andreabenini/FatBottomedBoard/electronics/teensy++2.0.png

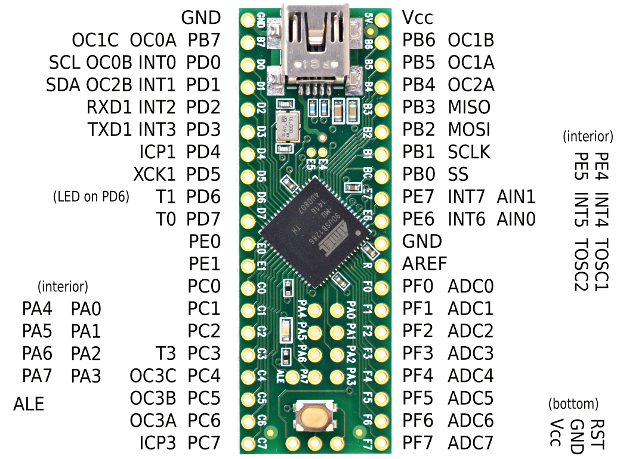
electronics/teensy++2.0.png
