andreabenini/FatBottomedBoard/badassmouse/bam-desk needle.stl

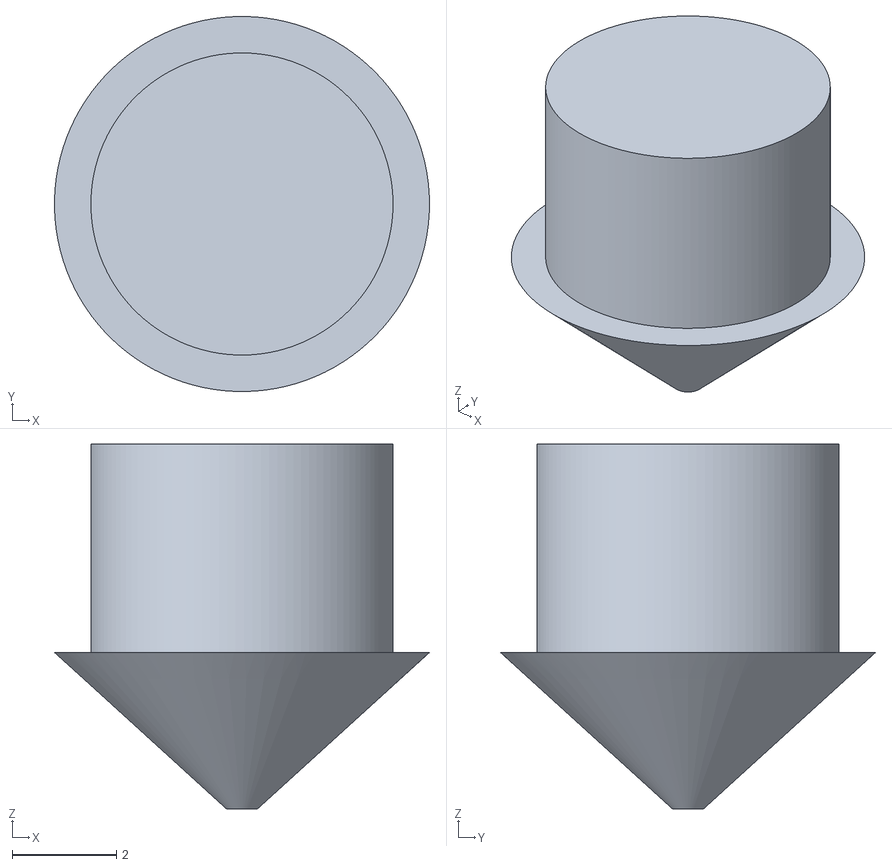
[picture p19: CAD file, 2025-08-23]
badassmouse/bam-desk needle.stl
7.20 x 7.20 x 7.00
