andreabenini/FatBottomedBoard/badassmouse/bam-wheel lock.stl

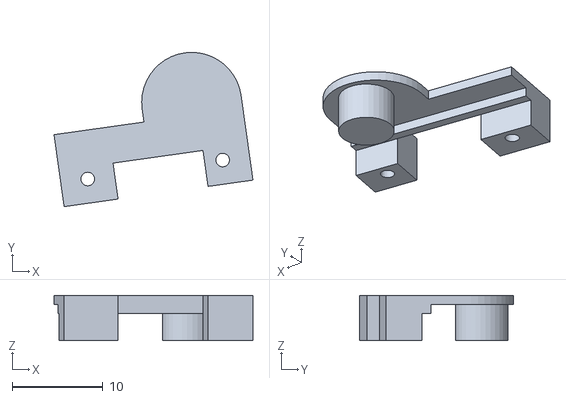
[picture p20: CAD file, 2025-08-15]
badassmouse/bam-wheel lock.stl
21.9 x 17.0 x 5.00
