andreabenini/FatBottomedBoard/badassmouse/bam-cable holder.stl

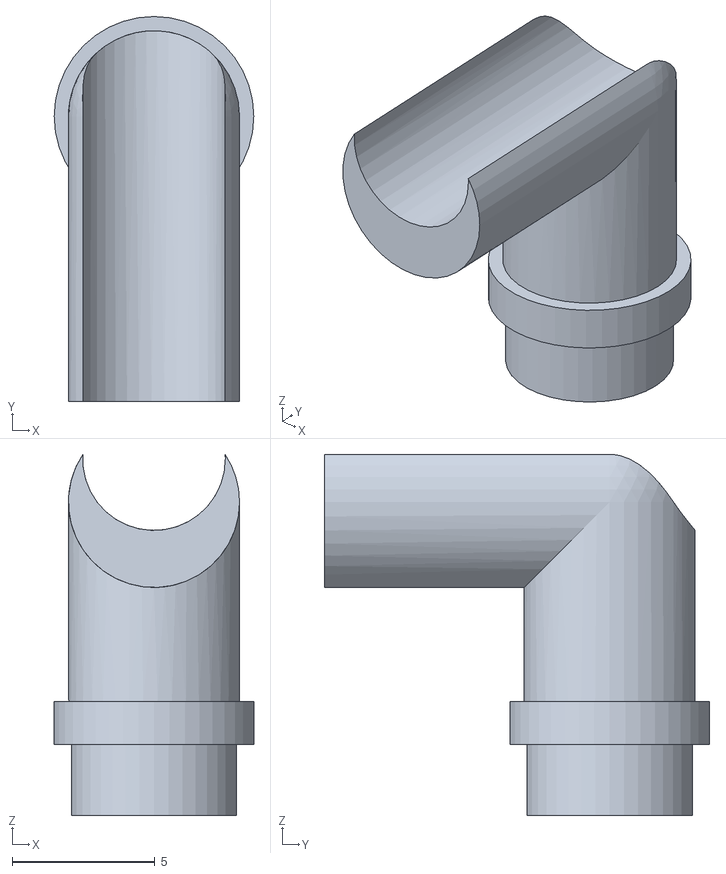
[picture p21: CAD file, 2025-08-13]
badassmouse/bam-cable holder.stl
7.00 x 13.5 x 12.7
