andreabenini/FatBottomedBoard/badassmouse/bam-scroll wheel holder.stl

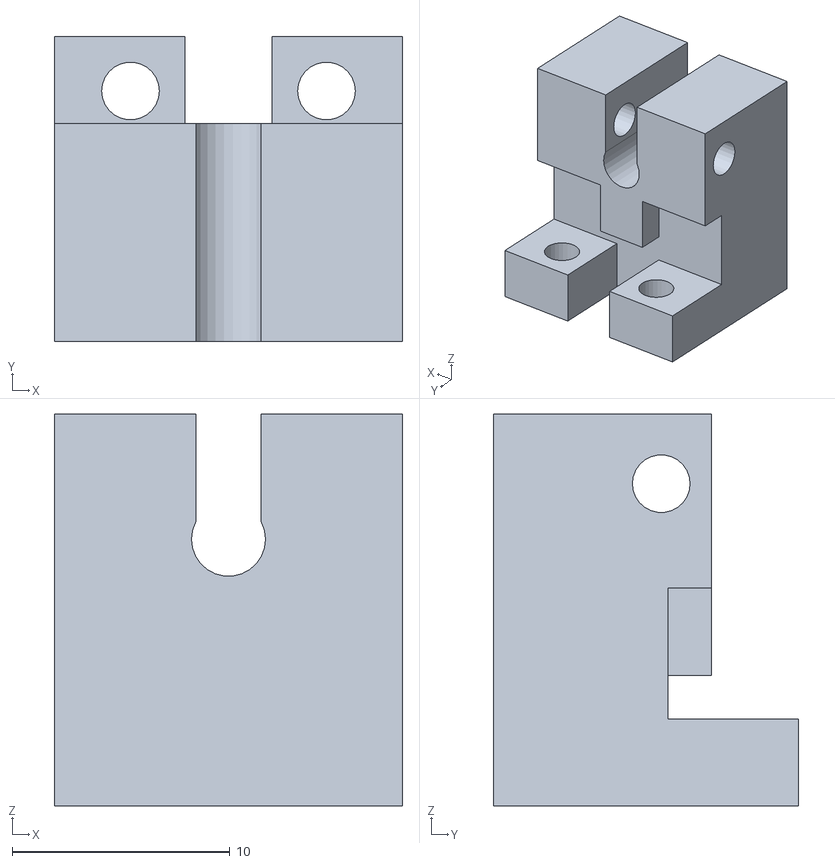
[picture p22: CAD file, 2025-08-13]
badassmouse/bam-scroll wheel holder.stl
16.0 x 14.0 x 18.0
