andreabenini/FatBottomedBoard/badassmouse/bam-support buttons.stl

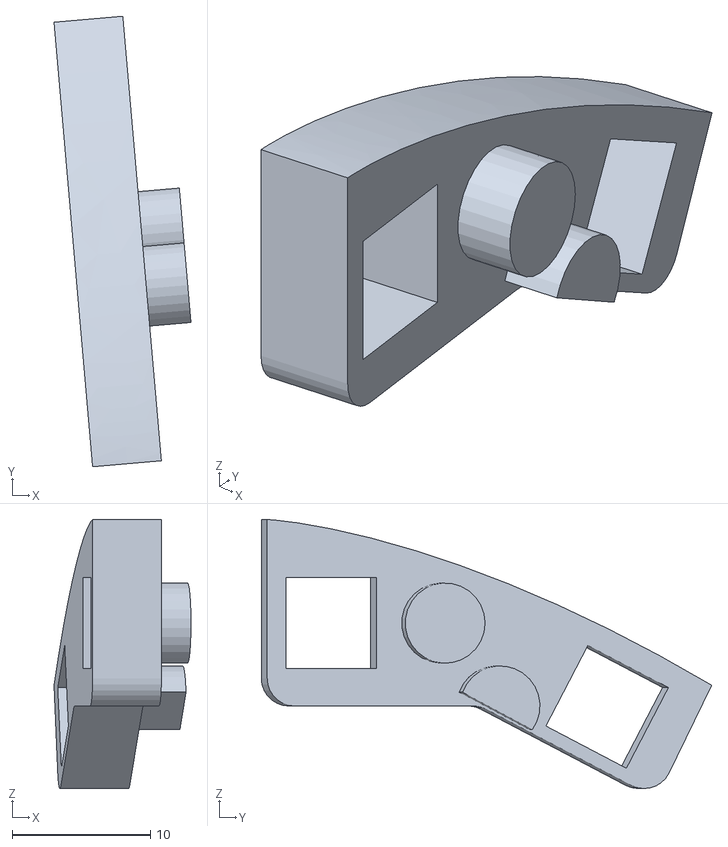
[picture p23: CAD file, 2025-08-09]
badassmouse/bam-support buttons.stl
9.92 x 32.6 x 19.5
