andreabenini/FatBottomedBoard/badassmouse/bam-USB cable holder.stl

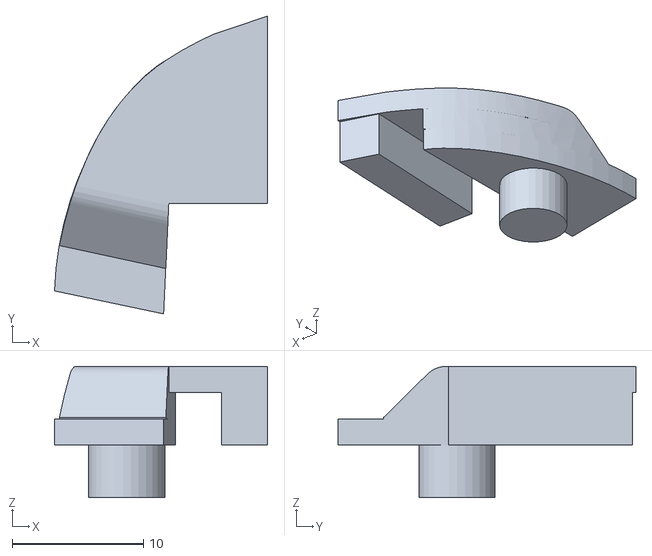
[picture p24: CAD file, 2025-08-09]
badassmouse/bam-USB cable holder.stl
16.2 x 22.7 x 10.0
