andreabenini/FatBottomedBoard/badassmouse/bam-partition back.stl

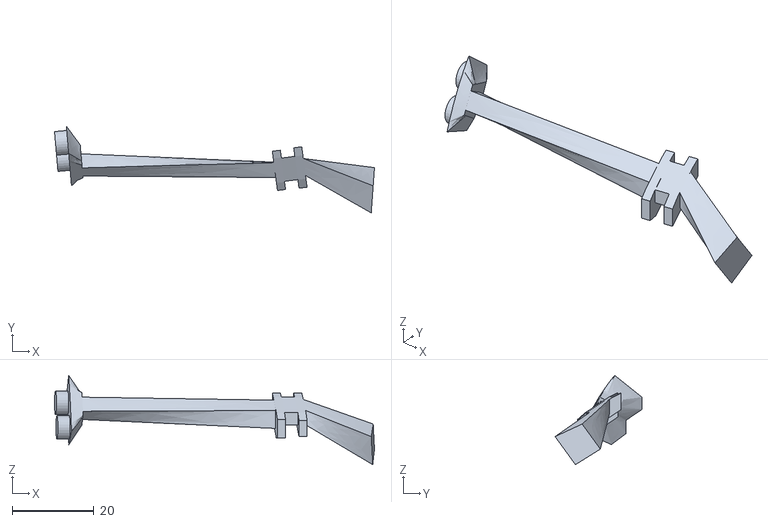
[picture p25: CAD file, 2025-08-08]
badassmouse/bam-partition back.stl
78.4 x 21.3 x 21.9
