andreabenini/FatBottomedBoard/badassmouse/bam-partition pinky right 1.stl

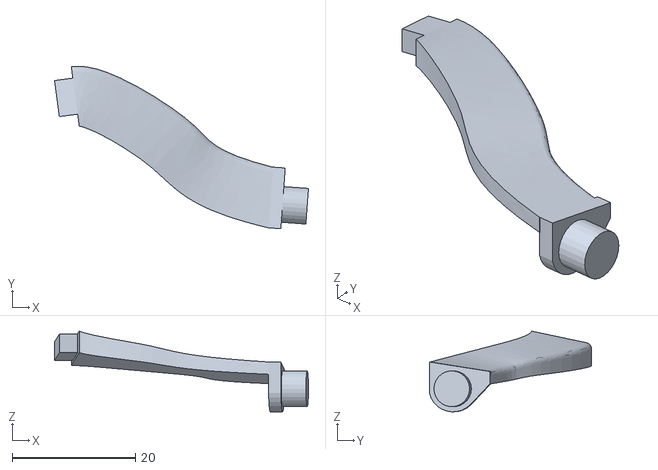
[picture p26: CAD file, 2025-08-06]
badassmouse/bam-partition pinky right 1.stl
41.2 x 26.4 x 13.1
