andreabenini/FatBottomedBoard/badassmouse/bam-bridge right.stl

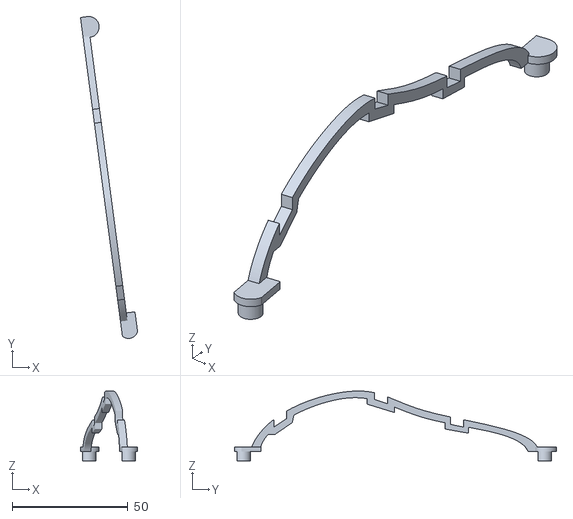
[picture p27: CAD file, 2025-08-06]
badassmouse/bam-bridge right.stl
24.6 x 138.9 x 30.1
