andreabenini/FatBottomedBoard/badassmouse/bam-support 3rd button.stl

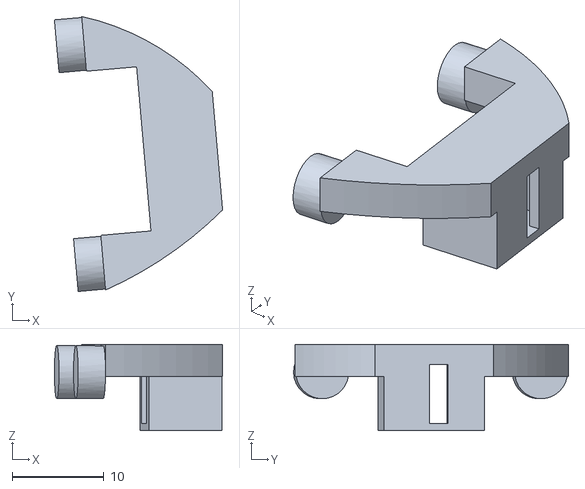
[picture p28: CAD file, 2025-08-04]
badassmouse/bam-support 3rd button.stl
18.4 x 30.0 x 9.45
