andreabenini/FatBottomedBoard/badassmouse/bam-bridge left.stl

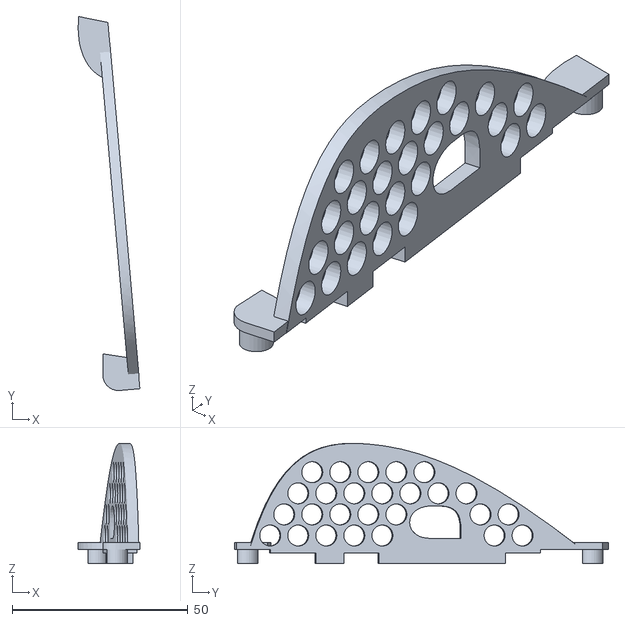
[picture p29: CAD file, 2025-08-04]
badassmouse/bam-bridge left.stl
17.6 x 106.3 x 34.2
