andreabenini/FatBottomedBoard/badassmouse/bam-bridge pinky.stl

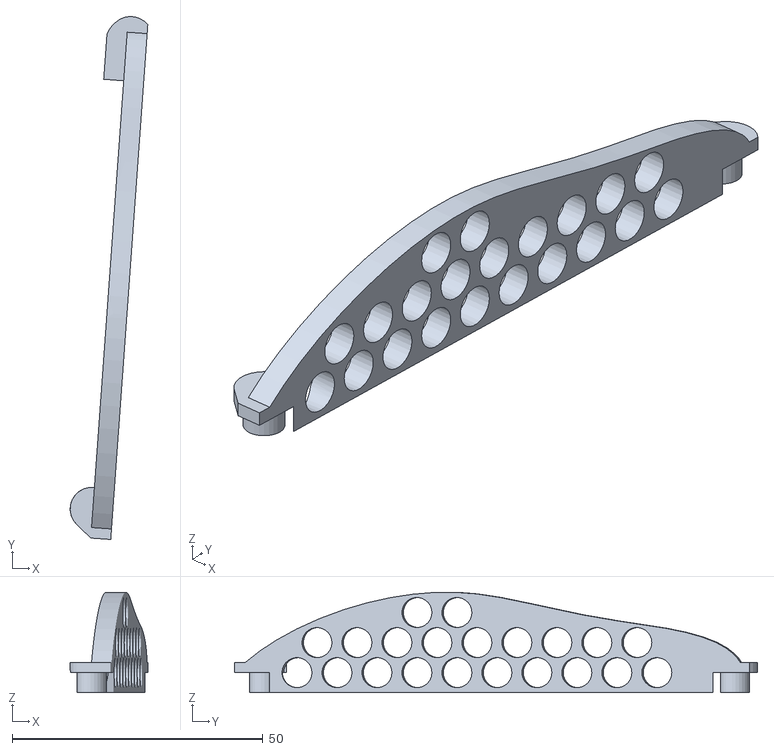
[picture p30: CAD file, 2025-08-04]
badassmouse/bam-bridge pinky.stl
15.5 x 104.4 x 20.0
