andreabenini/FatBottomedBoard/badassmouse/bam-3rd button.stl

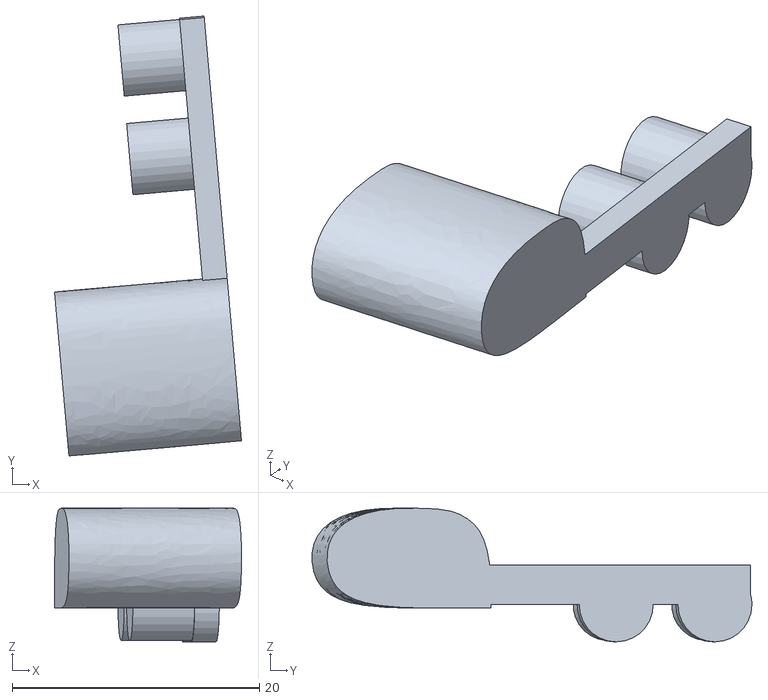
[picture p31: CAD file, 2025-08-04]
badassmouse/bam-3rd button.stl
15.1 x 35.6 x 10.8
