andreabenini/FatBottomedBoard/badassmouse/bam-pcb holder.stl

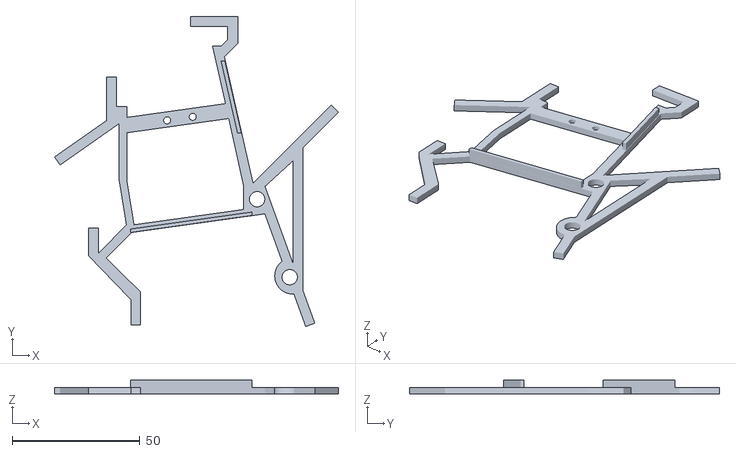
[picture p32: CAD file, 2025-07-30]
badassmouse/bam-pcb holder.stl
111.1 x 121.3 x 5.50
