andreabenini/FatBottomedBoard/badassmouse/bam-Palm connection.stl

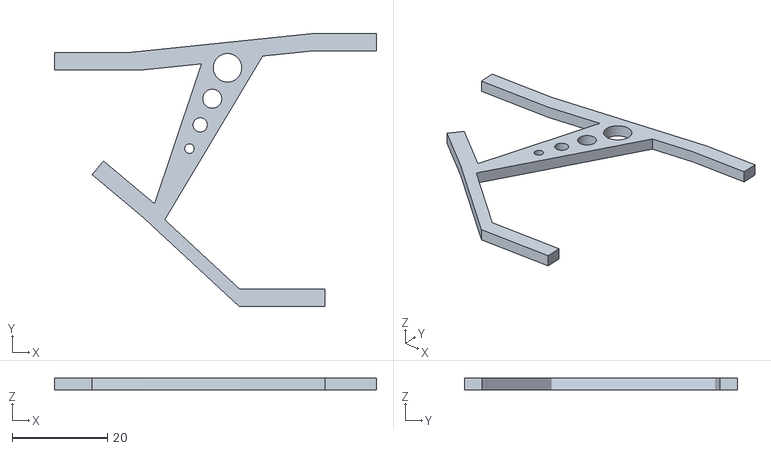
[picture p33: CAD file, 2025-07-30]
badassmouse/bam-Palm connection.stl
67.8 x 57.5 x 2.50
