andreabenini/FatBottomedBoard/badassmouse/bam-Ring and Pinky.stl

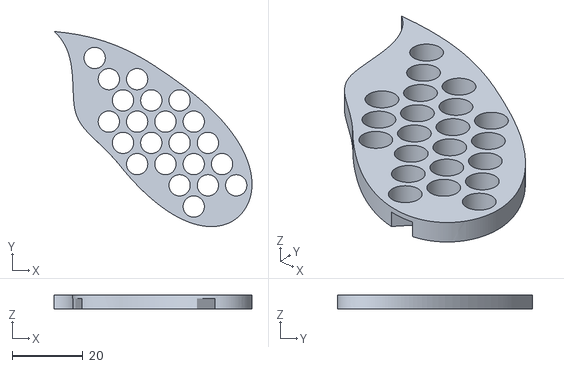
[picture p34: CAD file, 2025-07-29]
badassmouse/bam-Ring and Pinky.stl
56.0 x 55.2 x 4.00
