andreabenini/FatBottomedBoard/badassmouse/bam-Left and Right.stl

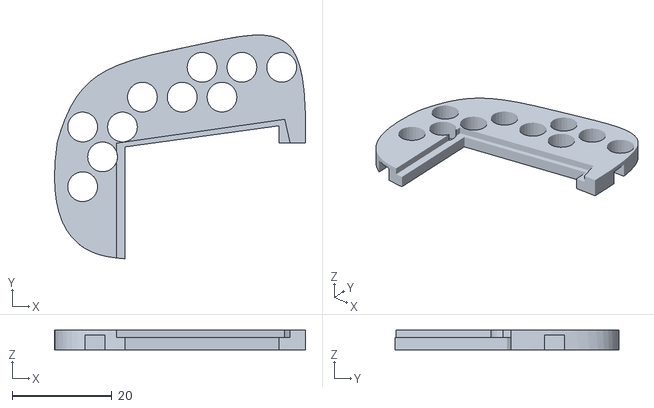
[picture p35: CAD file, 2025-07-29]
badassmouse/bam-Left and Right.stl
50.4 x 45.0 x 4.00
