andreabenini/FatBottomedBoard/badassmouse/bam-Thumb.stl

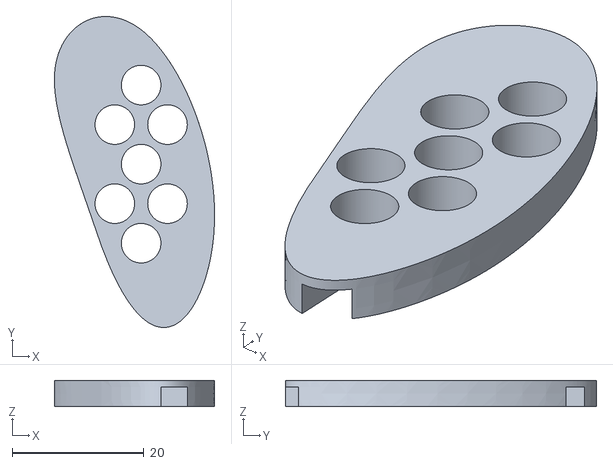
[picture p36: CAD file, 2025-07-13]
badassmouse/bam-Thumb.stl
24.3 x 47.2 x 4.00
