andreabenini/FatBottomedBoard/badassmouse/bam-Palm Left.stl

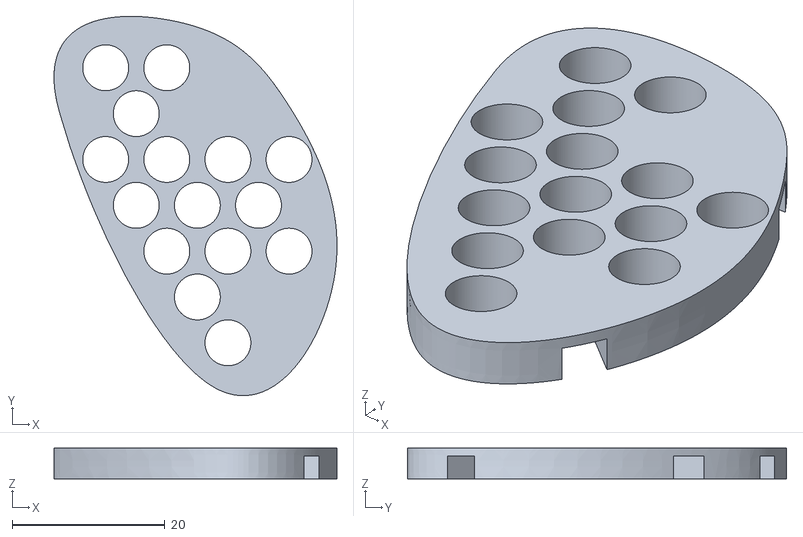
[picture p37: CAD file, 2025-07-13]
badassmouse/bam-Palm Left.stl
37.0 x 49.6 x 4.00
