andreabenini/FatBottomedBoard/badassmouse/bam-Palm Right.stl

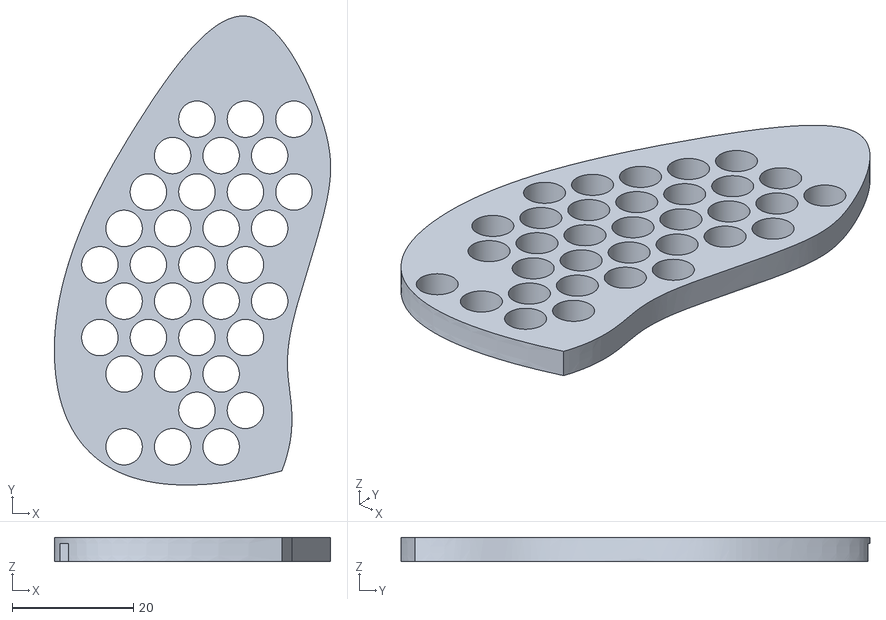
[picture p38: CAD file, 2025-07-13]
badassmouse/bam-Palm Right.stl
45.6 x 77.3 x 4.00
