andreabenini/FatBottomedBoard/software/keyboard/qmk_firmware/docs/feature_thermal_printer.md

# Thermal Printer

<!-- FIXME: Describe thermal printers support here. -->

## Thermal Printer Keycodes

|Key |Description |
|---|---|
|`PRINT_ON` |Start printing everything the user types|
|`PRINT_OFF`|Stop printing everything the user types |
