andreabenini/FatBottomedBoard/electronics/wiring_pinout2h.png

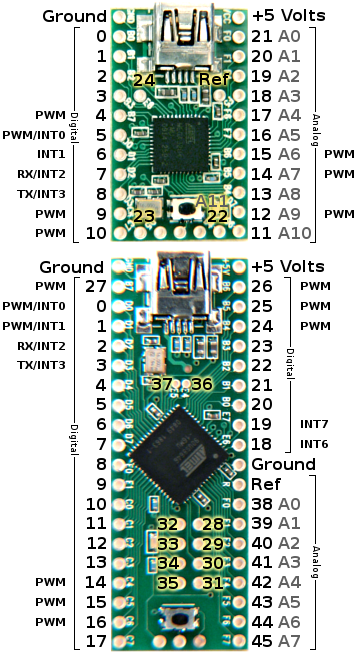
electronics/wiring_pinout2h.png
