andreabenini/FatBottomedBoard/electronics/32U4.sch

## KiCad design electronics/32U4.sch (2020-04-27)

Schematic: 32U4.sch

Parts:
1.8": TFT LCD ST7735S
Control: Rotary_Encoder_Switch
J1: Input 5v
Password: Rotary_Encoder_Switch
U1: Pro Micro 32U4 USB

Notes on the sheet:
LED SCK SDA A0 RESET CS GND VCC
Display Controller
AVR 32U4 Keyboard Controller LCD TFT Display Rotary Encoders
GND Vcc
SCK MISO MOSI CS
