andreabenini/FatBottomedBoard/electronics/Controller.sch

## KiCad design electronics/Controller.sch (2020-08-20)

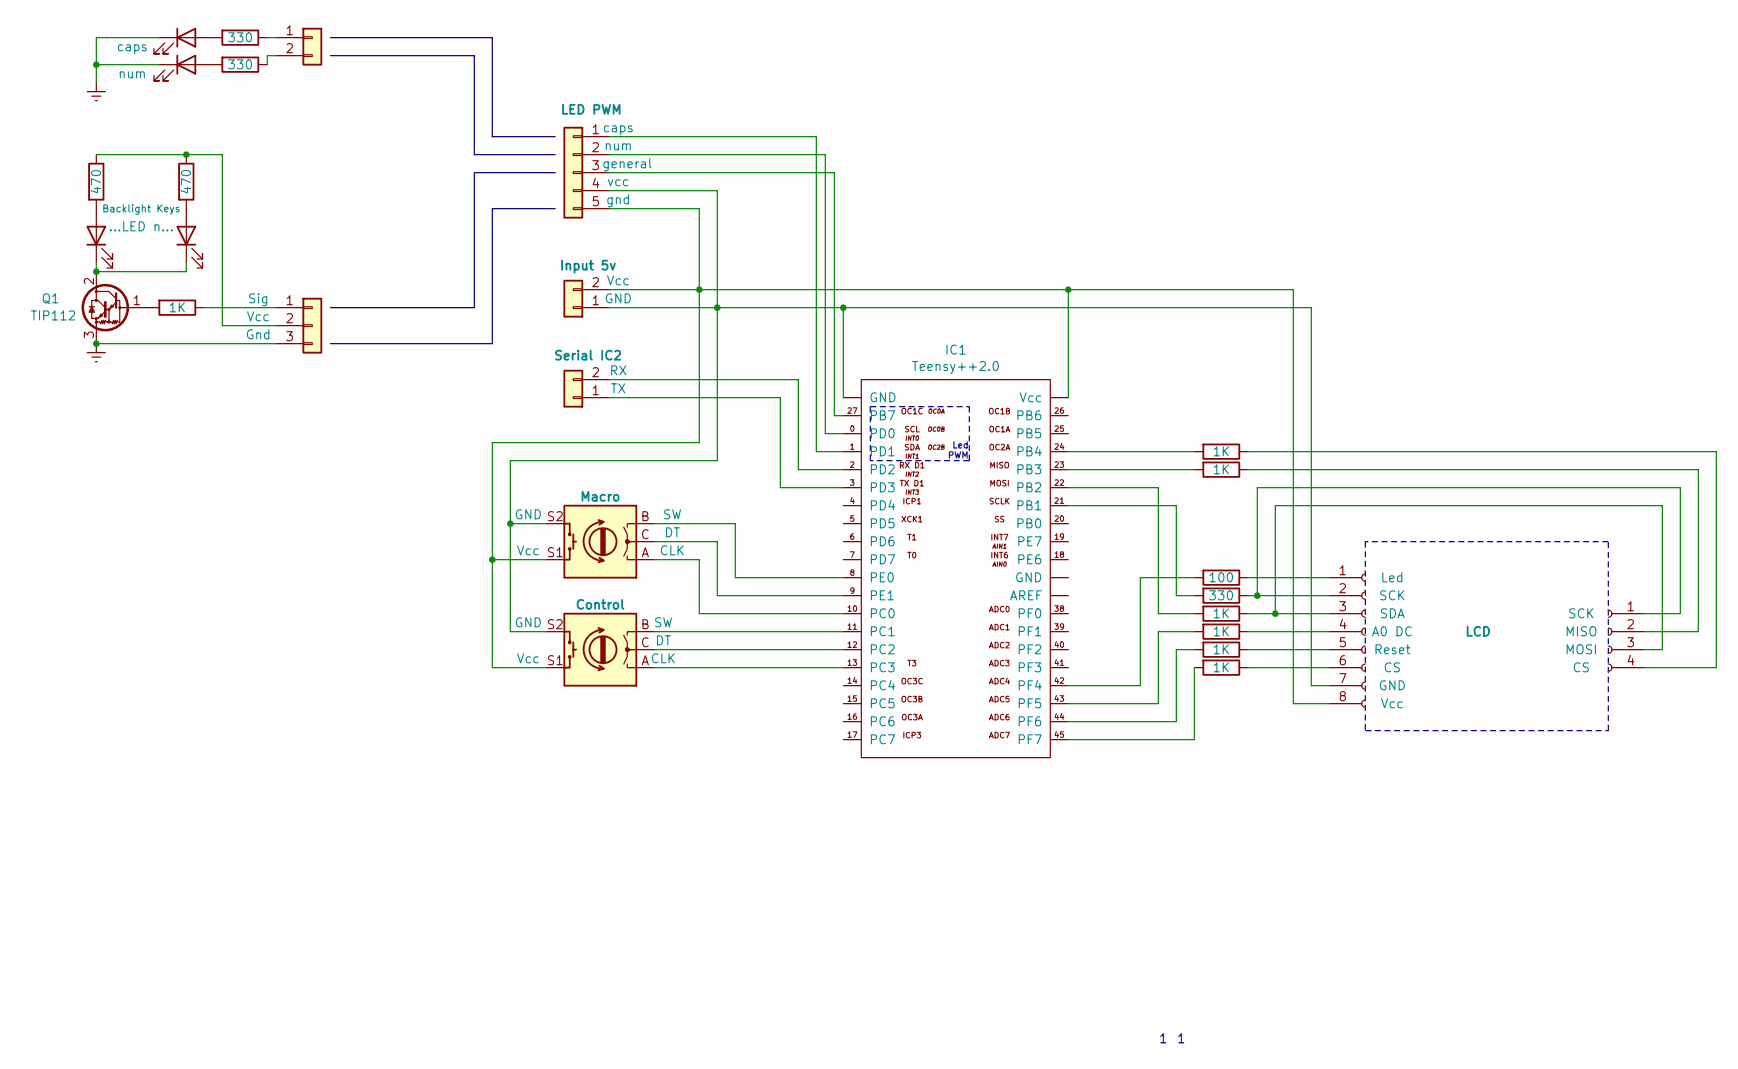
[picture p83: schematic Controller.sch]

Parts:
...LED.n...: LED
Control: Rotary_Encoder_Switch
IC1: Teensy++2.0
J1: Input 5v
LCD: 8 pin
Macro: Rotary_Encoder_Switch
Q1: TIP112; TO-220-3_Vertical
_: LED
caps: LED
num: LED

Connections:
GNDREF: Q1.3 (E), caps.1 (K), num.1 (K)
unnamed: ...LED.n....1 (K), Q1.2 (C), _.1 (K)
unnamed: Control.A, IC1.13 (PC3)
unnamed: Control.B, IC1.11 (PC1)
unnamed: Control.C, IC1.12 (PC2)
unnamed: Control.S1, IC1.~ (AREF), J1.2, LCD.8, Macro.S1
unnamed: Control.S2, IC1.~ (AREF), J1.1, LCD.7, Macro.S2
unnamed: IC1.8 (PE0), Macro.B
unnamed: IC1.9 (PE1), Macro.C
unnamed: IC1.10 (PC0), Macro.A

Notes on the sheet:
Led PWM
