andreabenini/FatBottomedBoard/electronics/Keyboard.sch

## KiCad design electronics/Keyboard.sch (2020-07-11)

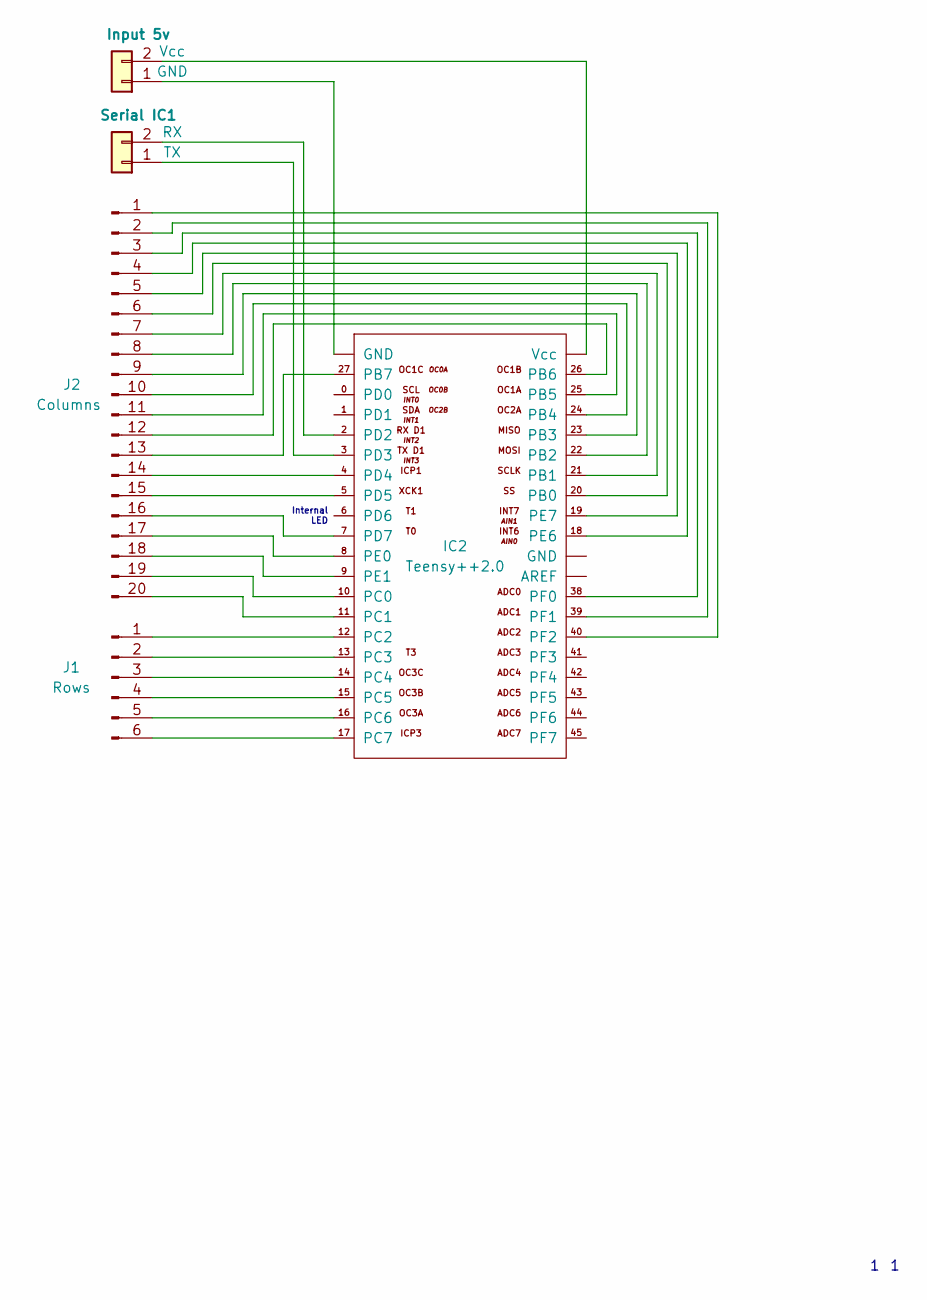
[picture p84: schematic Keyboard.sch]

Parts:
IC2: Teensy++2.0
J1: Input 5v
J2: Columns

Connections:
unnamed: IC2.4 (PD4), J2.14
unnamed: IC2.5 (PD5), J2.15
unnamed: IC2.7 (PD7), J2.16
unnamed: IC2.8 (PE0), J2.17
unnamed: IC2.9 (PE1), J2.18
unnamed: IC2.10 (PC0), J2.19
unnamed: IC2.11 (PC1), J2.20
unnamed: IC2.12 (PC2), J1.1
unnamed: IC2.13 (PC3), J1.2
unnamed: IC2.14 (PC4), J1.3
unnamed: IC2.15 (PC5), J1.4
unnamed: IC2.16 (PC6), J1.5
unnamed: IC2.17 (PC7), J1.6
unnamed: IC2.18 (PE6), J2.4
unnamed: IC2.19 (PE7), J2.5
unnamed: IC2.20 (PB0), J2.6
unnamed: IC2.21 (PB1), J2.7
unnamed: IC2.22 (PB2), J2.8
unnamed: IC2.23 (PB3), J2.9
unnamed: IC2.24 (PB4), J2.10
unnamed: IC2.25 (PB5), J2.11
unnamed: IC2.26 (PB6), J2.12
unnamed: IC2.27 (PB7), J2.13
unnamed: IC2.38 (PF0), J2.3
unnamed: IC2.39 (PF1), J2.2
unnamed: IC2.40 (PF2), J2.1
unnamed: IC2.~ (AREF), J1.1, J1.2

Notes on the sheet:
Internal LED
