andreabenini/FatBottomedBoard/software/keyboard/config/fatbottomedboard/fatbottomedboard.c

/** Copyright 2020 Ben
 *
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
 * You should have received a copy of the GNU General Public License
 * along with this program.  If not, see <http://www.gnu.org/licenses/>.
 */
#include "fatbottomedboard.h"

/**
 * Serial globals
 */
// These buffers may be any size from 2 to 256 bytes.
#define RX_BUFFER_SIZE 64
#define TX_BUFFER_SIZE 40

static volatile uint8_t tx_buffer[TX_BUFFER_SIZE];
static volatile uint8_t tx_buffer_head;
static volatile uint8_t tx_buffer_tail;
static volatile uint8_t rx_buffer[RX_BUFFER_SIZE];
static volatile uint8_t rx_buffer_head;
static volatile uint8_t rx_buffer_tail;

osType osTypeCurrent;           // Current operating system (default: linux)

/**/


// Optional override functions below.
// You can leave any or all of these undefined.
// These are only required if you want to perform custom actions.

/**
 * put your keyboard start-up code here, runs once when the firmware starts up
 */
void matrix_init_kb(void) {
    uart_init(9600);
    matrix_init_user();
}

/**
 * put your looping keyboard code here
 * runs every cycle (a lot)
 */
void matrix_scan_kb(void) {
    matrix_scan_user();
}

/**
 * put your per-action keyboard code here
 * runs for every action, just before processing by the firmware
 */
bool process_record_kb(uint16_t keycode, keyrecord_t *record) {
    return process_record_user(keycode, record);
}

// put your keyboard LED indicator (ex: Caps Lock LED) toggling code here
void led_set_kb(uint8_t usb_led) {
    led_set_user(usb_led);
}


// Send current keboard layout to display
void layout(const char *str) {
    _delay_ms(100);
    uart_putchar('l');
    _delay_ms(20);
    uart_print_P_delay(str);
    uart_putchar('\n');
} /**/


/**
 * OS FUNCTIONS
 */


/**
 * OS TOGGLE - Change current OS (and key behavior as well)
 */
void osToggle(void) {
    switch (osTypeCurrent) {
    case LINUX:
        osChange(MACOS);
        break;
    case MACOS:
        osChange(WIN);
        break;
    case WIN:
    default:
        osChange(LINUX);
        break;
    }
    osSend();
} /**/


/**
 * OS CHANGE - Change current OS (and key behavior as well)
 * @see Do NOT use this function to change the OS, use osToggle() instead.
 *      osToggle() calls this function internally
 */
void osChange(osType osDefault) {
    osTypeCurrent = osDefault;
} /**/


// Send OS information through serial port to the other controller
void osSend(void) {
    _delay_ms(100);
    uart_putchar('o');
    _delay_ms(20);
    switch (osTypeCurrent) {
    case LINUX:
        uart_print_P_delay(PSTR("Linux"));
        break;
    case MACOS:
        uart_print_P_delay(PSTR("MacOS"));
        break;
    case WIN:    
    default:
        uart_print_P_delay(PSTR("Windows"));
        break;
    }
    uart_putchar('\n');
} /**/


// Return selected OS
osType osCurrent(void) {
    return osTypeCurrent;
} /**/


/**
 * SERIAL FUNCTIONS (communicate with the other teensy board)
 */


// Initialize the UART
void uart_init(uint32_t baud) {
    cli();
    UBRR1 = (F_CPU / 4 / baud - 1) / 2;
    UCSR1A = (1 << U2X1);
    UCSR1B = (1 << RXEN1) | (1 << TXEN1) | (1 << RXCIE1);
    UCSR1C = (1 << UCSZ11) | (1 << UCSZ10);
    tx_buffer_head = tx_buffer_tail = 0;
    rx_buffer_head = rx_buffer_tail = 0;
    sei();
} /**/

// Transmit a byte
void uart_putchar(uint8_t c) {
    uint8_t i;
    i = tx_buffer_head + 1;
    if (i >= TX_BUFFER_SIZE) {
        i = 0;
    }
    while (tx_buffer_tail == i) ; // wait until space in buffer
    //cli();
    tx_buffer[i] = c;
    tx_buffer_head = i;
    UCSR1B = (1 << RXEN1) | (1 << TXEN1) | (1 << RXCIE1) | (1 << UDRIE1);
    //sei();
} /**/

// Send a byte to serial port
void uart_print_P(const char *str) {
    char c;
    while (1) {
        c = pgm_read_byte(str++);
        if (!c) {
            break;
        }
        uart_putchar(c);
    }
} /**/

// Send a byte to serial port and wait (20ms, fixed)
void uart_print_P_delay(const char *str) {
    char c;
    while (1) {
        c = pgm_read_byte(str++);
        if (!c) {
            break;
        }
        uart_putchar(c);
        _delay_ms(20);
    }
} /**/

// Receive a byte
uint8_t uart_getchar(void) {
    uint8_t c, i;
    while (rx_buffer_head == rx_buffer_tail) ; // wait for character
    i = rx_buffer_tail + 1;
    if (i >= RX_BUFFER_SIZE) {
        i = 0;
    }
    c = rx_buffer[i];
    rx_buffer_tail = i;
    return c;
} /**/

// Return the number of bytes waiting in the receive buffer.
// Call this before uart_getchar() to check if it will need
// to wait for a byte to arrive.
uint8_t uart_available(void) {
    uint8_t head, tail;
    head = rx_buffer_head;
    tail = rx_buffer_tail;
    if (head >= tail) {
        return head - tail;
    }
    return RX_BUFFER_SIZE + head - tail;
} /**/

// Transmit Interrupt
ISR(USART1_UDRE_vect) {
    uint8_t i;
    if (tx_buffer_head == tx_buffer_tail) {
        // buffer is empty, disable transmit interrupt
        UCSR1B = (1 << RXEN1) | (1 << TXEN1) | (1 << RXCIE1);
    } else {
        i = tx_buffer_tail + 1;
        if (i >= TX_BUFFER_SIZE) {
            i = 0;
        }
        UDR1 = tx_buffer[i];
        tx_buffer_tail = i;
    }
} /**/

// Receive Interrupt
ISR(USART1_RX_vect) {
    uint8_t c, i;
    c = UDR1;
    i = rx_buffer_head + 1;
    if (i >= RX_BUFFER_SIZE) {
        i = 0;
    }
    if (i != rx_buffer_tail) {
        rx_buffer[i] = c;
        rx_buffer_head = i;
    }
} /**/
