andreabenini/FatBottomedBoard/software/keyboard/config/fatbottomedboard/fatbottomedboard.h

/**
 * Copyright 2020 Ben
 *
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
 */
#pragma once
#include "quantum.h"

/**
 * This is a shortcut to help you visually see your layout.
 *
 * - First section contains all of the arguments representing the physical layout of the board and position of the keys.
 * - Second section converts the arguments into a two-dimensional array which represents the switch matrix.
 */
#define LAYOUT( \
	K000, K001, K002, K003, K004, K005, K006, K007, K008, K009, K010, K011, K012, K013, K114, K014, K015, K016, K017, K018, K019, \
	K100, K101, K102, K103, K104, K205, K105, K106, K107, K108, K109, K110, K111, K112, K213, K113, K214, K215, K115, K216, K117, K118, K119, \
	K200, K201, K202, K203, K204, K305, K206, K307, K207, K208, K209, K210, K211, K212, K313, K414, K314, K315, K416, K316, K217, K218, \
	K300, K301, K302, K303, K304, K405, K306, K407, K408, K308, K309, K310, K311, K312, K413, K417, K317, K318, K219, \
	K400, K401, K402, K403, K404, K505, K406, K507, K508, K409, K509, K410, K411, K412, K415, K517, K518, K418, \
	K500, K501, K502, K503, K504, K506, K510, K511, K512, K513, K514, K515, K516, K519, K419, K319  \
) { \
	{ K000,  K001,  K002,  K003,  K004,  K005,  K006,  K007,  K008,  K009,  K010,  K011,  K012,  K013,  K014,  K015,  K016,  K017,  K018,  K019 }, \
	{ K100,  K101,  K102,  K103,  K104,  K105,  K106,  K107,  K108,  K109,  K110,  K111,  K112,  K113,  K114,  K115,  KC_NO, K117,  K118,  K119 }, \
	{ K200,  K201,  K202,  K203,  K204,  K205,  K206,  K207,  K208,  K209,  K210,  K211,  K212,  K213,  K214,  K215,  K216,  K217,  K218,  K219 }, \
	{ K300,  K301,  K302,  K303,  K304,  K305,  K306,  K307,  K308,  K309,  K310,  K311,  K312,  K313,  K314,  K315,  K316,  K317,  K318,  K319 }, \
	{ K400,  K401,  K402,  K403,  K404,  K405,  K406,  K407,  K408,  K409,  K410,  K411,  K412,  K413,  K414,  K415,  K416,  K417,  K418,  K419 }, \
	{ K500,  K501,  K502,  K503,  K504,  K505,  K506,  K507,  K508,  K509,  K510,  K511,  K512,  K513,  K514,  K515,  K516,  K517,  K518,  K519 }  \
}


typedef enum osType {
    LINUX,
    MACOS,
    WIN
} osType;


// display defines
void layout(const char *str);

// OS defines
void osChange(osType osDefault);
void osToggle(void);
void osSend(void);
osType osCurrent(void);
// Serial defines
void uart_init(uint32_t baud);
void uart_putchar(uint8_t c);
#define uart_print(s) uart_print_P(PSTR(s))
void uart_print_P(const char *str);
void uart_print_P_delay(const char *str);
uint8_t uart_getchar(void);
uint8_t uart_available(void);
