andreabenini/FatBottomedBoard/software/controller/src/gamepong.h

#ifndef GAMEPONG_H
#define GAMEPONG_H
#include <Arduino.h>
#include <TFT.h>

#include "main.h"
#include "defines.h"
#include "display.h"


void gamepongPage();
void gamepongLoop();
void gamepongAction(byte Action);


#endif
