andreabenini/FatBottomedBoard/software/controller/buildHooks.py

#!/usr/bin/env python
# -*- coding: utf-8 -*-
#
# pylint: disable=undefined-variable
#
# This script is executed by PlatformIO before compiling the code, it's some sort of hook executed
# before everything in order to manually patch few things
#   - Make a backup copy of usb_hid/usb_private.h -> usb_hid/usb_private.h.backup (just once, the first time)
#       It's commented but you can resume it if you're running for the first time
#   - Change: VID,PID,Name in the usb_hid profile (file: usb_private.h)
# Slightly modified version: it creates a backup only if it does not exist yet
#
import os
import shutil
Import("env", "projenv")

deviceVID  = "0x08de"
devicePID  = "0xbabe"
deviceName = "Ben KeyController"

# Edit USB device information
def editUSBsettings(fileName):
    # Search and replace inside the file
    fHandler = open(fileName, "rt")
    data = fHandler.read()
    data = data.replace("0x16C0", deviceVID)                            # Replace all occurrences of the original Vendor  ID (VID)
    data = data.replace("0x0482", devicePID)                            # Replace all occurrences of the original Product ID (PID)
    data = data.replace("Teensy Keyboard/Mouse/Joystick", deviceName)   # Replace all occurrences of the original Device  Name
    fHandler.close()
    # Reopen the input file in write mode
    fHandler = open(fileName, "wt")
    #overrite the input file with the resulting data
    fHandler.write(data)
    #close the file
    fHandler.close()

# Move back the original file
def buildPostAction(source, target, env):
    shutil.move(fileNameBackup, fileName)


# Before compilation (BEGIN)
print("----------------------------------------------- Compilation setup [BEGIN]")
# usb_private.h backup
fileName = os.path.sep.join([env['CPPPATH'][1]]+["usb_hid","usb_private.h"])
fileNameBackup = fileName+".backup"
if not os.path.exists(fileNameBackup):
    shutil.copyfile(fileName, fileNameBackup)
editUSBsettings(fileName)
print("----------------------------------------------- Compilation setup [ END ]")
shutil.copyfile(".pio/build/teensy2pp/firmware.hex", "fatbottomedboard_code.hex")

env.AddPostAction("buildprog", buildPostAction)
